makespacemadrid/Jarvis/Diseños3D/MakeSwitch/FreeCad/STL/DualColor/carcasa-mitades/bottom-a.obj

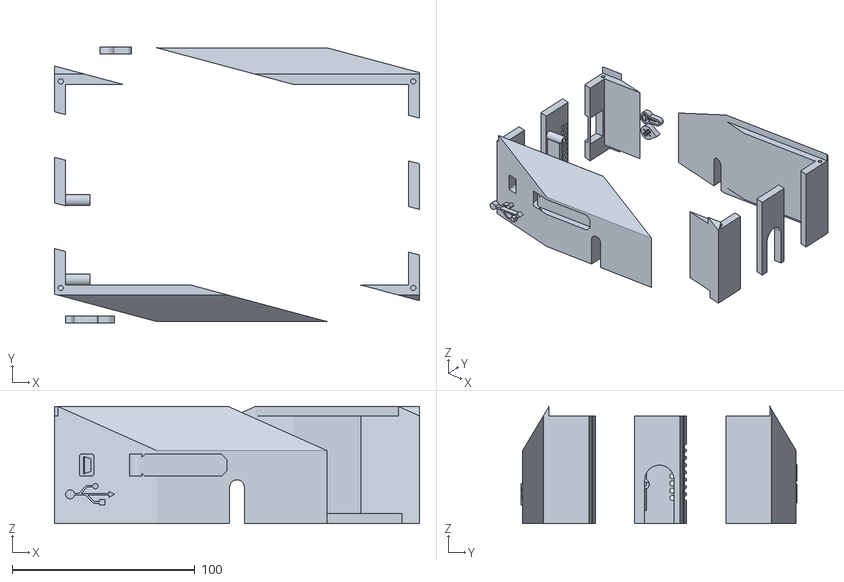
[picture p16: CAD file, 2015-12-14]
Diseños3D/MakeSwitch/FreeCad/STL/DualColor/carcasa-mitades/bottom-a.obj
200.0 x 151.3 x 64.2
