makespacemadrid/Jarvis/Diseños3D/MakeSwitch/FreeCad/STL/DualColor/carcasa_make-amarillo (repaired).stl

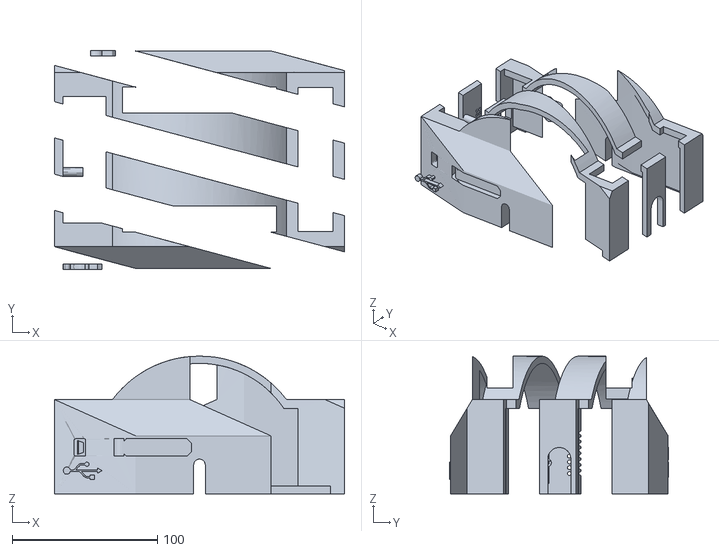
[picture p17: CAD file, 2015-11-29]
Diseños3D/MakeSwitch/FreeCad/STL/DualColor/carcasa_make-amarillo (repaired).stl
200.0 x 151.3 x 94.9
