makespacemadrid/Jarvis/Diseños3D/MakeSwitch/FreeCad/STL/palanca.obj

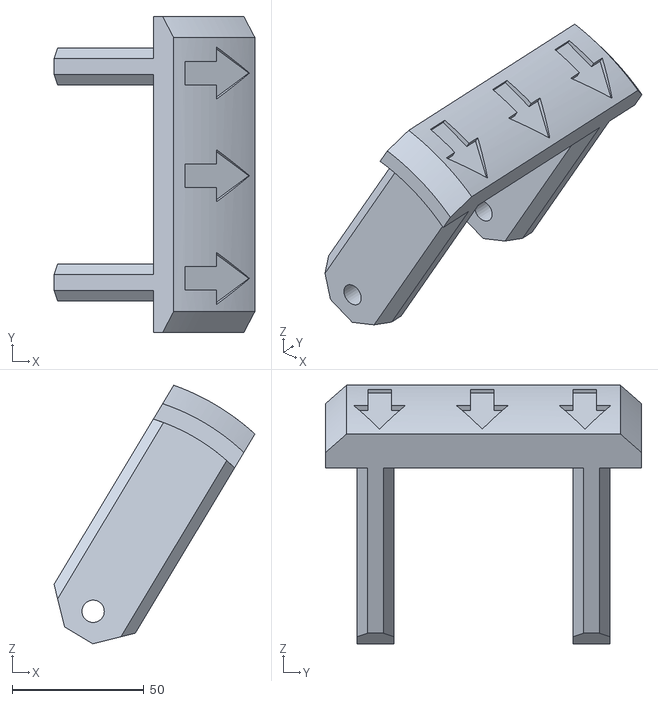
[picture p18: CAD file, 2015-11-29]
Diseños3D/MakeSwitch/FreeCad/STL/palanca.obj
76.3 x 120.0 x 98.2
