makespacemadrid/Jarvis/Diseños3D/MakeSwitch/FreeCad/STL/base.obj

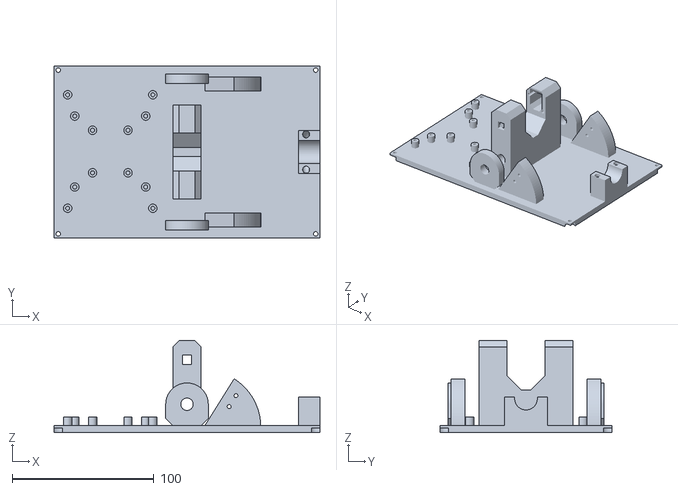
[picture p19: CAD file, 2015-11-29]
Diseños3D/MakeSwitch/FreeCad/STL/base.obj
187.5 x 121.5 x 65.0
