makespacemadrid/Jarvis/Diseños3D/MakeSwitch/FreeCad/STL/DualColor/carcasa-mitades/top.amf

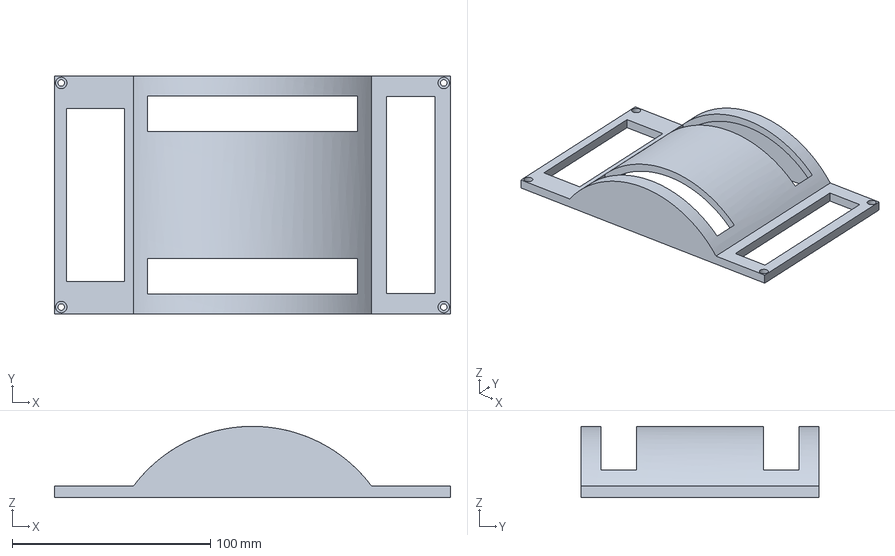
[picture p20: CAD file, 2015-12-14]
Diseños3D/MakeSwitch/FreeCad/STL/DualColor/carcasa-mitades/top.amf
200.0 x 120.0 x 36.0 mm
