makespacemadrid/Jarvis/Diseños3D/MakeSwitch/FreeCad/STL/DualColor/letras-transparente.obj

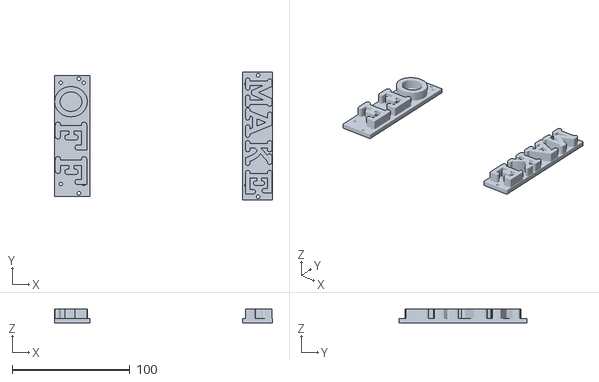
[picture p21: CAD file, 2015-11-29]
Diseños3D/MakeSwitch/FreeCad/STL/DualColor/letras-transparente.obj
185.4 x 108.9 x 12.0
