makespacemadrid/Jarvis/Diseños3D/MakeSwitch/FreeCad/STL/DualColor/carcasa-mitades/bottom-b (repaired).stl

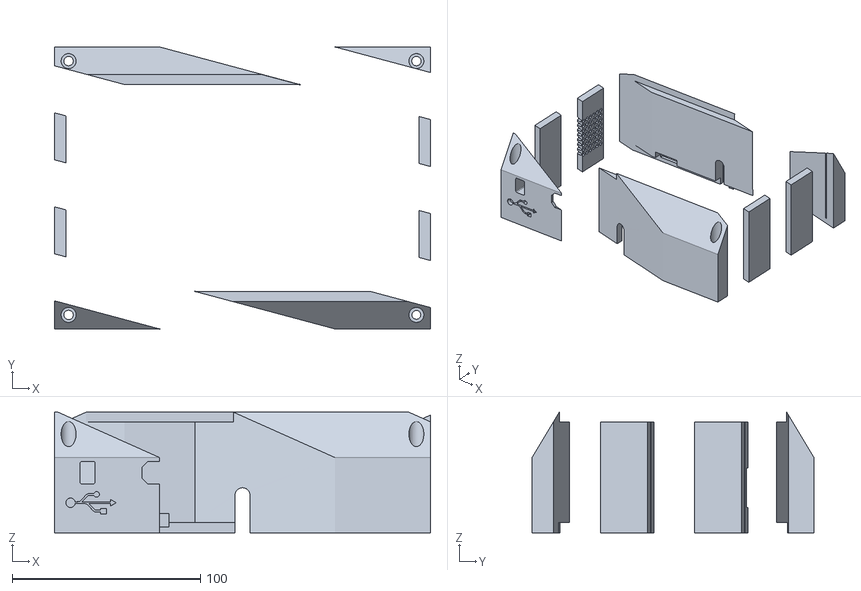
[picture p22: CAD file, 2015-12-14]
Diseños3D/MakeSwitch/FreeCad/STL/DualColor/carcasa-mitades/bottom-b (repaired).stl
200.0 x 150.0 x 64.2
