makespacemadrid/Jarvis/Diseños3D/MakeSwitch/FreeCad/STL/DualColor/palanca-flechas.obj

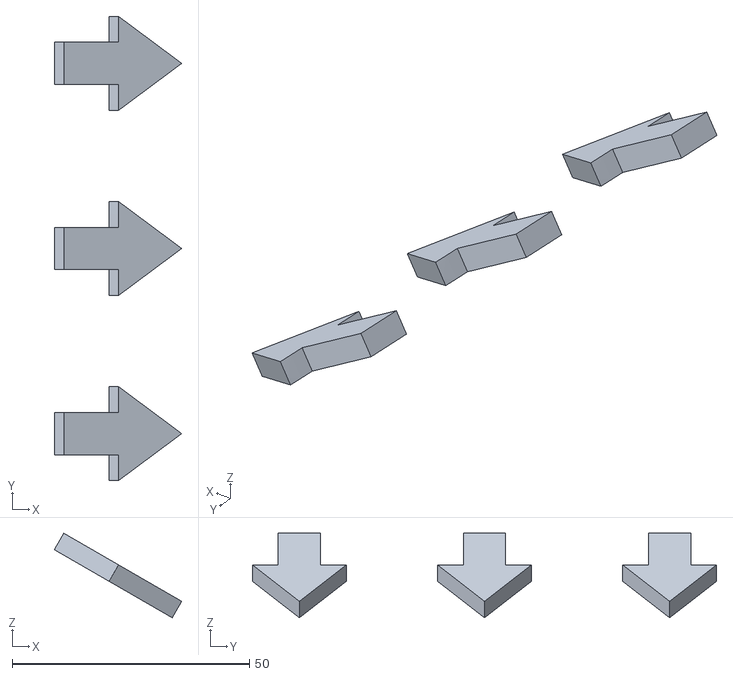
[picture p23: CAD file, 2015-11-29]
Diseños3D/MakeSwitch/FreeCad/STL/DualColor/palanca-flechas.obj
26.9 x 97.8 x 17.8
