makespacemadrid/Jarvis/Diseños3D/MakeSwitch/FreeCad/STL/reten.obj

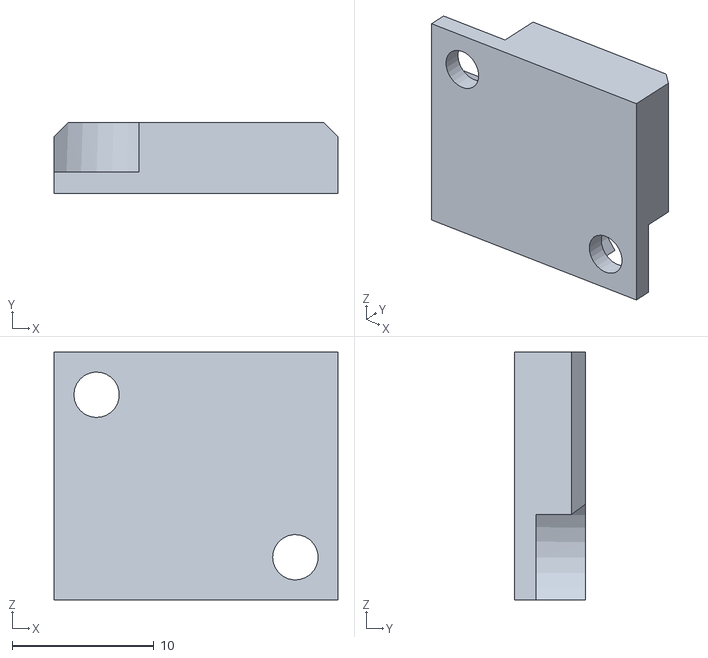
[picture p24: CAD file, 2015-11-29]
Diseños3D/MakeSwitch/FreeCad/STL/reten.obj
20.0 x 5.00 x 17.4
