makespacemadrid/Jarvis/Diseños3D/MakeSwitch/FreeCad/STL/empujador.obj

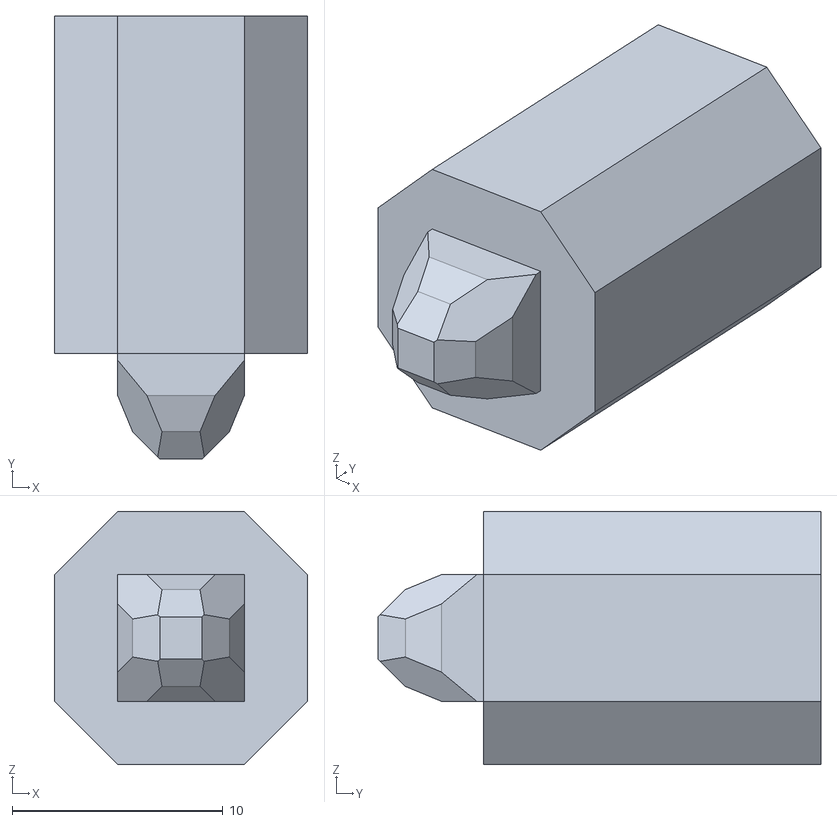
[picture p25: CAD file, 2015-11-29]
Diseños3D/MakeSwitch/FreeCad/STL/empujador.obj
12.0 x 21.0 x 12.0
