makespacemadrid/Jarvis/Diseños3D/MakeSwitch/FreeCad/STL/DualColor/carcasa-mitades/bottom-b.obj

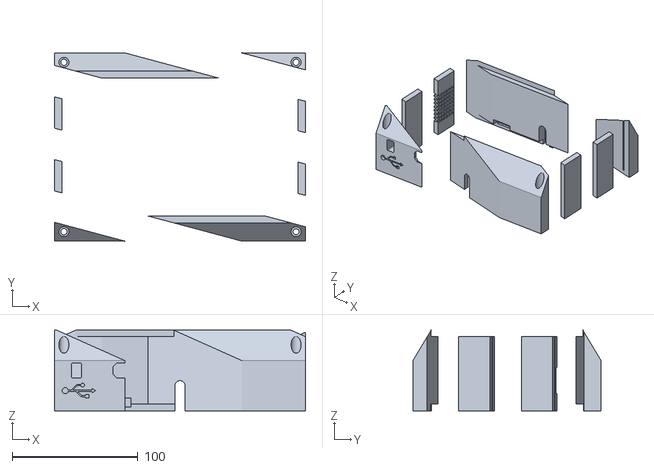
[picture p26: CAD file, 2015-12-14]
Diseños3D/MakeSwitch/FreeCad/STL/DualColor/carcasa-mitades/bottom-b.obj
200.0 x 150.0 x 64.2
