makespacemadrid/Jarvis/Diseños3D/MakeSwitch/FreeCad/STL/DualColor/letras-opaco.obj

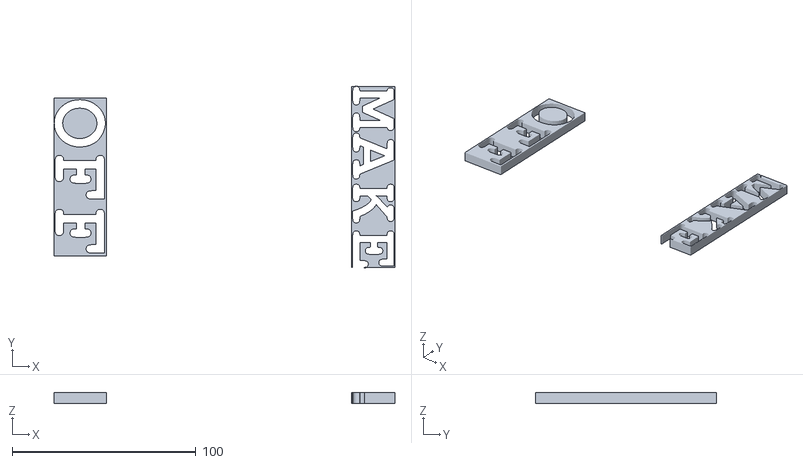
[picture p27: CAD file, 2015-11-29]
Diseños3D/MakeSwitch/FreeCad/STL/DualColor/letras-opaco.obj
185.4 x 98.6 x 6.00
