makespacemadrid/Jarvis/Software/JarvisFirmware/ws2812led.h

#ifndef LED
#define LED


#include <Adafruit_NeoPixel.h> //WTF hay que hacer el include en el ino!
#include <vector>
#include "nodeComponent.h"
//#include "ledMatrixIcons.h"

class ws2812Strip {
public:
    class led{ // clase led dentro de la clase Strip
    public:
      led(int r = 0, int g = 0, int b = 0, float bright = 1.0): m_r(r), m_g(r), m_b(b), m_bright(bright) {;}

      void setColor(uint8_t red =0,uint8_t green=0,uint8_t blue=0)
      {
          m_r = red;
          m_g = green;
          m_b = blue;
      }

      void dimm(int power)
      {
          float p = power /100;
          dimm(p);
      }

      void dimm(float factor = 0.75)
      {
          m_r *= factor;
          m_g *= factor;
          m_b *= factor;
      }

      void setBrightness(float b = 1.0)
      {
          m_bright = b;
      }

      void off()   {setColor(0,0,0);}
      void white() {setColor(200,200,200);}
      void red()   {setColor(230,0,0);}
      void green() {setColor(0,230,0);}
      void blue()  {setColor(0,0,230);}

      void setR(uint8_t val) {m_r = val;}
      void setG(uint8_t val) {m_g = val;}
      void setB(uint8_t val) {m_b = val;}

      int r()   {return m_r * m_bright;}
      int g()   {return m_g * m_bright;}
      int b()   {return m_b * m_bright;}

    private:
      uint8_t m_r;
      uint8_t m_g;
      uint8_t m_b;
      float   m_bright;
    };
  
  ws2812Strip(int pin = -1, int lednr = 25, float bright = 1.0) : m_pin(pin) , m_pixels(lednr, pin, NEO_GRB + NEO_KHZ800)
  {
    m_brightness = bright;
    if((isValid()))
    {
      for(int i = 0 ; i < lednr ; i++) m_leds.push_back(led());
    }
  }

  void setBrightness(int b)
  {
      m_brightness = b/100.0f;
      update();
  }

  void setBrightness(float b = 1.0)
  {
      m_brightness = b;
      update();
  }

  float brightness()
  {
      return m_brightness;
  }

  bool isValid() {return  (m_pin != -1);}

  std::vector<led> leds()&   {return m_leds;}

  led* getLed(int pos)
  {
    return &m_leds[pos];
  }

  void setup()
  {
    if(!isValid()) return;
    Serial.println("Setting up ws2812 strip....");
    m_pixels.begin();
    yield();
    test();
    off();
  }
  
  void update(){
    if(!isValid()) return;
    for(int i=0;i<m_leds.size();i++)
    {
        m_pixels.setPixelColor(i, (m_leds[i].r() * m_brightness) ,
                                  (m_leds[i].g() * m_brightness) ,
                                  (m_leds[i].b() * m_brightness) );
    }

    yield();
    m_pixels.show(); 
  }

  void off()
  {
    if(!isValid()) return;
    for( uint16_t i = 0 ; i < m_leds.size() ; i++)
    {
        m_leds[i].off();
    }
    update();
  }

  void setColor(uint8_t r,uint8_t g, uint8_t b){
    if(!isValid()) return;     
    for(int i=0;i<m_leds.size();i++)
    {
      m_leds[i].setColor(r,g,b);
    }
    update();
  }

  void test()
  {
    if(!isValid()) return;
    for( uint16_t i = 0 ; i < m_leds.size() ; i++)
    {
      m_leds[i].setColor(20,20,20);
      if(i%2 == 0)update();
    }
  }

private:
    std::vector<led>    m_leds;
    int                 m_pin;
    float               m_brightness;
    Adafruit_NeoPixel   m_pixels;
};


class ledGadget :  public nodeComponent
{
  public:
    enum animationType
    {
        animationNone,
        animationFade,
        animationGlow,
        animationBlink,
        animationCylon,
        animationChaoticLight,
        animationRainbow,
        animationScroll
    };

    ledGadget(ws2812Strip* m_parentStrip): m_strip(m_parentStrip) , m_bright(1.0)
    {
      m_capableEvents.push_back(E_ACTIVATED);
      m_capableEvents.push_back(E_DEACTIVATED);
      m_actions.push_back(A_ACTIVATE);
      m_actions.push_back(A_DEACTIVATE);
      m_actions.push_back(A_DIMM);
      m_actions.push_back(A_SET_COLOR);
      m_actions.push_back(A_SET_LEDS);
      m_actions.push_back(A_CYLON);
      m_actions.push_back(A_GLOW);
      m_actions.push_back(A_FADE);
    }
    
    void update()
    {
      if(!m_enabled) return;
      animate();
    }

    bool isValid() {return m_strip->isValid();}

    void deactivate()
    {
        fade();
    }

//gestion del array de leds

    void setLeds(std::vector<String>&  args)
    {
      if(!m_enabled) return;
      m_animationType = animationNone;
      for(int i = 0 ; i < args.size(); i+=3)
      {
          int n = i/3;
          if( n <= m_leds.size())
          {
            ws2812Strip::led* l = m_leds[n];
            l->setColor(args[i].toInt(),args[i+1].toInt(),args[i+2].toInt());
          }
      }
    }

    void setLeds(std::vector<uint8_t>  args)
    {
      if(!m_enabled) return;
      m_animationType = animationNone;
      for(int i = 0 ; i < args.size(); i+=3)
      {
          int n = i/3;
          if( n <= m_leds.size())
          {
            uint8_t r = args[i];
            uint8_t g = args[i+1];
            uint8_t b = args[i+2];
            ws2812Strip::led* l = m_leds[n];
            l->setColor(r,g,b);
          }
      }
    }

    void addLed(ws2812Strip::led* nLed)
    {
        m_leds.push_back(nLed);
    }

    void addLed(int start,int count,bool reverseOrder = false)
    {
        if(reverseOrder)
        {
            for(int i = start+count-1 ; i >= start ; i-- )
            {
                m_leds.push_back(m_strip->getLed(i));
            }
        }
        else
        {
            for(int i = start ; i < start+count ; i++ )
            {
                m_leds.push_back(m_strip->getLed(i));
            }
        }
    }

//efectos y animaciones

    virtual void off()
    {
        if(!m_enabled) return;
        resetAnimation();
        for(int i = 0 ; i < m_leds.size() ; i++)
            m_leds[i]->off();
        m_strip->update();
    }

    virtual void setColor(uint8_t r, uint8_t g, uint8_t b)
    {

        if(!m_enabled) return;
        resetAnimation();
        for(int i = 0 ; i < m_leds.size() ; i++)
        {
            m_leds[i]->setColor(r,g,b);
        }
        m_strip->update();
    }

    void dimm(uint8_t power)
    {
        if(power > 100) power = 100;
        setBrightness(power /100.0f);
    }

    void setBrightness(float b = 1.0)
    {
        m_bright = b;
        for(int i = 0 ; i < m_leds.size() ; i++)
        {
            m_leds[i]->setBrightness(b);
        }
        m_strip->update();
    }

    virtual void resetAnimation()
    {
        if(m_animationType == animationGlow)
        {
            setBrightness(1.0);
        }

        m_animationType = animationNone;
        m_counter1 = 0, m_counter2 = 0 ; m_counter3 = 0;
    }

    virtual void fade()
    {
        resetAnimation();
        m_animationType = animationFade;
    }

    virtual void glow()
    {
        resetAnimation();
        m_counter1 = 50, m_counter2 = 1 ; m_counter3 = 50;
        m_animationType = animationGlow;
    }

    virtual void blink()
    {
        resetAnimation();
        m_counter1 = 0, m_counter2 = 0 ; m_counter3 = 0;
        m_animationType = animationBlink;
    }

    virtual void cylon()
    {//animacion cylon
        resetAnimation();
        m_counter1 = 0, m_counter2 = 0 ; m_counter3 = 0;
        m_animationType = animationCylon;
    }

    virtual void chaoticLight()
    {
        resetAnimation();
        m_counter1 = 0, m_counter2 = 0 ; m_counter3 = 0;
        m_animationType = animationChaoticLight;
    }

    virtual void rainbow()
    {
        resetAnimation();
        m_counter1 = 0, m_counter2 = 0 ; m_counter3 = 0;
        m_animationType = animationRainbow;
    }

    virtual void scroll()
    {
        resetAnimation();
        m_counter1 = 0, m_counter2 = 0 ; m_counter3 = 0;
        m_animationType = animationScroll;
    }


    virtual void animate()
    {
        if(!m_enabled) return;
        if      (m_animationType == animationNone)
        {
            return;
        }else if(m_animationType == animationFade)
        {
            animateFade();
        }else if(m_animationType == animationGlow)
        {
            animateGlow();
        }else if(m_animationType == animationBlink)
        {
            animateBlink();
        }else if(m_animationType == animationCylon)
        {
            animateCylon();
        }else if(m_animationType == animationChaoticLight)
        {
            animateChaoticLigth();
        }else if(m_animationType == animationRainbow)
        {
            animateRainbow();
        }else if(m_animationType == animationScroll)
        {
            animateScroll();
        }

        m_strip->update();
    }


  protected:
    ws2812Strip*                    m_strip;
    std::vector<ws2812Strip::led*>  m_leds;
    animationType                   m_animationType = animationNone;
    float m_bright;

    uint8_t m_counter1;
    uint8_t m_counter2;
    uint8_t m_counter3;


    virtual void animateFade()
    {
        bool all_off = true;
        for(int i = 0 ; i < m_leds.size() ; i++)
        {
            if( (m_leds[i]->r() > 0) || (m_leds[i]->g() > 0) || (m_leds[i]->b() > 0) )
            {
                m_leds[i]->dimm();
                all_off=false;
            }
        }

        if(all_off)
        {
            m_events.push_back(E_DEACTIVATED);
            resetAnimation();
        }
    }

    virtual void animateGlow()
    {//contador 1 se usa contar la iteracion, y el 2 para la direccion(sumando/restando).
        if(m_counter2 == 0)
        {//sumando
            float bright = m_counter1/50.0;
            for(int i = 0 ; i < m_leds.size() ; i++)
            {
                m_leds[i]->setBrightness(bright);
            }

            if(m_counter1 == 50)
              m_counter2 = 1;
            else
              m_counter1++;
        }
        else
        {//restando
            float bright = m_counter1/50.0;
            for(int i = 0 ; i < m_leds.size() ; i++)
            {
                m_leds[i]->setBrightness(bright);
            }

            if(m_counter1 == 0)
                m_counter2 = 0;
            else
              m_counter1--;
        }
 //       Serial.print("C1: ");
 //       Serial.print(m_counter1);
 //       Serial.print(" :C2: ");
 //       Serial.print(m_counter2);
 //       Serial.print(" :C3: ");
 //       Serial.println(m_counter3);
 //       Serial.println("   ");
 //       Serial.println(m_leds[0]->b);
    }

    virtual void animateBlink()
    {

    }

    virtual void animateCylon()
    {//contador 1 para la iteracion, 2 para la direccion
        int min = 0;
        int max = m_leds.size();
        int count = max - min;

        if(m_counter2 == 0)//incrementando
        {
            int i = 0;
            for(int l = min ; l < max ; l++ )
            {
                ws2812Strip::led *led = m_leds[l];
                if(i == m_counter1)
                {
                   led->setColor(255,0,0);
                }
                else
                {
                    led->dimm();
                }

                if(m_counter1 >= max)
                {
                    m_counter1 = max;
                    m_counter2 = 1;
                    return;
                }
                else
                {
                    i++;
                }
            }
            m_counter1++;
        }else //decrementando
        {
            int i = count;
            for(int l = max-1 ; l >= min ; l-- )
            {
                ws2812Strip::led *led = m_leds[l];
                if(i == m_counter1)
                {
                   led->setColor(255,0,0);
                }
                else
                {
                    led->dimm();
                }

                if(m_counter1 <= min)
                {
                    m_counter1 = 0;
                    m_counter2 = 0;
                    return;
                }
                else
                {
                    i--;
                }
            }
            m_counter1--;
        }
    }
    virtual void animateChaoticLigth()
    {
        for(int i = 0 ; i < m_leds.size() ; i++)
        {
            int random = rand() % 3;
            if(random == 0)
                m_leds[i]->red();
            else if(random == 1)
                m_leds[i]->green();
            else if(random == 2)
                m_leds[i]->blue();
        }
    }


    virtual void animateRainbow()
    {
        if(m_counter1 > 256*5) m_counter1 = 0;

        for(uint16_t i = 0;  i < m_leds.size() ; i++)
        {
            uint16_t WheelPos = 255 - (((i * 256 / m_leds.size()) + m_counter1) & 255);
            if(WheelPos < 85)
            {
                m_leds[i]->setColor(255 - WheelPos * 3, 0, WheelPos * 3);
            }
            else if(WheelPos < 170)
            {
                WheelPos -= 85;
                m_leds[i]->setColor(0, WheelPos * 3, 255 - WheelPos * 3);
            }
            else
            {
                WheelPos -= 170;
                m_leds[i]->setColor(WheelPos * 3, 255 - WheelPos * 3, 0);
            }
            yield();
        }
        m_counter1 += 10;
    }

    virtual void animateScroll() {;}
};

class ledBar : public ledGadget
{
public:
    ledBar(ws2812Strip* parentStrip) : ledGadget(parentStrip), m_reversed(false) 
    {
      m_id = "ledBar";
    }
    void setReversed(bool reversed) {m_reversed = reversed;}

protected:
    bool m_reversed;

};


class ledStatusTrio : public ledBar
{
  public:
    ledStatusTrio(ws2812Strip* m_parentStrip, uint8_t mControllerLed, uint8_t wifiLed, uint8_t extraLed) :
       ledBar(m_parentStrip)
    {
        m_id = "ledStatusTrio";
        m_controllerLed = m_strip->getLed(mControllerLed);
        m_wifiLed       = m_strip->getLed(wifiLed);
        m_extraLed      = m_strip->getLed(extraLed);
        addLed(m_controllerLed);
        addLed(m_wifiLed);
        addLed(m_extraLed);
    }

    void animate()
    {
        if(!m_enabled) return;
        ledBar::animate();

        if(m_statusDecay)
            m_controllerLed->dimm();
        if(m_wifiStatusDecay)
            m_wifiLed->dimm();
        if(m_extraLedDecay)
            m_extraLed->dimm();
        m_strip->update();
    }

    void controllerInit()
    {
        if(!m_enabled)return;
        m_statusDecay = false;
        m_controllerLed->setColor(0,100,100);
    }

    void controllerOK()
    {
        if(!m_enabled)return;
        m_statusDecay = true;
        m_controllerLed->setColor(0,100,0);
    }

    void controllerError()
    {
        if(!m_enabled)return;
        m_statusDecay = false;
        m_controllerLed->setColor(100,0,0);
    }

    void wifiTX()
    {
        if(!m_enabled)return;
        m_wifiStatusDecay = true;
        m_wifiLed->setColor(0,100,0);
    }

    void wifiRX()
    {
        if(!m_enabled)return;
        m_wifiStatusDecay = true;
        m_wifiLed->setColor(100,0,0);
    }

    void wifiInit()
    {
        if(!m_enabled)return;
        m_wifiStatusDecay = false;
        m_wifiLed->setColor(100,100,0);
    }

    void wifiClient()
    {
        if(!m_enabled)return;
        m_wifiStatusDecay = false;
        m_wifiLed->setColor(0,100,100);
        m_wifiStatusColor = *m_wifiLed;
    }

    void wifiAutoConfig()
    {
        if(!m_enabled)return;
        m_wifiStatusDecay = false;
        m_wifiLed->setColor(100,0,100);
        m_wifiStatusColor = *m_wifiLed;
    }

    void wifiOK()
    {
        if(!m_enabled)return;
        *m_wifiLed = m_wifiStatusColor;
    }

    void wifiError()
    {
        if(!m_enabled)return;
        m_wifiStatusDecay = false;
        m_wifiLed->setColor(100,0,0);
    }

    void extraLedOK()
    {
        if(!m_enabled)return;
        m_extraLed->setColor(0,200,0);
    }

    void extraLedIdle()
    {
        if(!m_enabled)return;
        m_extraLed->setColor(0,0,200);
    }

    void extraLedError()
    {
        if(!m_enabled)return;
        m_extraLed->setColor(200,0,0);
    }

    void extraLedSetDecay(bool decay)
    {
        if(!m_enabled)return;
        m_extraLedDecay = decay;
    }

  private:
    ws2812Strip::led*   m_controllerLed;
    ws2812Strip::led*   m_wifiLed;
    ws2812Strip::led*   m_extraLed;
    ws2812Strip::led    m_wifiStatusColor;

    bool                m_statusDecay     = false;
    bool                m_wifiStatusDecay = false;
    bool                m_extraLedDecay   = false;
};


class ledMatrix : public ledBar
{
public:
    ledMatrix(uint8_t firstLednr, uint8_t cols, uint8_t rows, ws2812Strip* parentStrip,bool mirror = false, bool invertEachRow = false) : ledBar(parentStrip)
    {
        m_actions.push_back(A_DISPLAY);
        //Serial.println("Init matrix");
        for(int r = 0 ; r < rows ; r++)
        {
            //Serial.print("*row#");
            //Serial.println(r);

            m_matrix.push_back(std::vector<ws2812Strip::led*>());
            bool invertedRow = invertEachRow&&(r % 2 != 0);
            if(mirror) invertedRow = !invertedRow;

            int start = r*cols+firstLednr;
            int count = cols;

            if(invertedRow)
            {
                for(int i = start+count-1 ; i >= start ; i-- )
                {
                    //Serial.print(",");
                    //Serial.print(i);
                    ws2812Strip::led* l = m_strip->getLed(i);
                    //l->red();
                    //m_strip->update();
                    m_leds.push_back(l);
                    m_matrix[r].push_back(l);
                }
            }
            else
            {
                for(int i = start ; i < start+count ; i++ )
                {
                    //Serial.print(",");
                    //Serial.print(i);
                    ws2812Strip::led* l = m_strip->getLed(i);
                    //l->green();
                    //m_strip->update();
                    m_leds.push_back(l);
                    m_matrix[r].push_back(l);
                }
            }
            //Serial.println(".");
            yield();
        }

        m_id = "ws2812Matrix-";
        m_id +=cols;
        m_id +="x";
        m_id += rows;
        this->glow();
    }

    void deactivate()
    {   
        ledGadget::deactivate();
    }


    void display(std::vector<String>& args)
    {
        std::vector<uint8_t> argsInt;
        while(args.size())
        {
            argsInt.push_back(args[0].toInt());
            args.erase(args.begin());
        }
        yield();
        display(argsInt);
    }

    void display(std::vector<uint8_t>& args)
    {
         resetAnimation();

         if(args.size()%5 != 0) return; // los argumentos tienen que venir de 5 en 5. (x,y,r,g,b)
         File f = SPIFFS.open("displayBuffer", "w+");
         if (!f) {
             Serial.println("file open failed: displayBuffer");
             return;
         }
         uint8_t frows,fcols;

         if(f.size() > 2)
         {
             frows = f.read();
             fcols = f.read();
         }
         else
         {
             frows = 0;
             fcols = 0;
             f.write(0);
             f.write(0);
         }

         while (args.size())
         {
             int row = args[0];
             args.erase(args.begin());
             int col = args[0];
             args.erase(args.begin());
             uint8_t r = args[0];
             args.erase(args.begin());
             uint8_t g = args[0];
             args.erase(args.begin());
             uint8_t b = args[0];
             args.erase(args.begin());


             if(row < m_matrix.size() && col < m_matrix[row].size())
                 m_matrix[row][col]->setColor(r,g,b);
         }
        yield();
//        if(m_scrollImg[0].size() > m_matrix[0].size())
//             scroll();

         Serial.print("L-display done:, fm:");
         Serial.println(getFreeMem());
         m_strip->update();
    }

    void displayMatrix(std::vector<std::vector<ws2812Strip::led> > matrix)
    {
        if(matrix.size() == 0) return;

        resetAnimation();

        off();

        if( (matrix.size() > m_matrix.size()) || (matrix[0].size() > m_matrix[0].size()))
        {
            //m_scrollImg = matrix;
        }
        else
        {
            for(uint8_t row = 0 ; row < matrix.size() ; row++) //copia los valores que estan dentro del rango de la matriz
            {
                for(uint8_t col = 0 ; col < matrix[row].size() ; col++)
                {
                    if((row < m_matrix.size()) && (col < m_matrix[row].size()))
                    {
                        *m_matrix[row][col] = matrix[row][col];
                    }
                }
            }
        }
        update();
    }

    void writeMatrixToFile(String filename,const std::vector<std::vector<ws2812Strip::led> >& matrix)
    {
        if(!m_matrix.size() || !m_matrix[0].size())
        {
            Serial.println("Bad Matrix");
            return;
        }
        File f = SPIFFS.open(filename, "w");
        if (!f) {
            Serial.println("file open failed");
            return;
        }

//        f.close();//esto deberia de vaciar el fichero
//        f = SPIFFS.open(filename, "a");
        Serial.println("File Opened for write");

        uint8_t rows,cols;
        rows = matrix.size();
        cols = matrix[0].size();
        Serial.print("Saving matrix, ");
        Serial.print(rows);
        Serial.print("x");
        Serial.print(cols);
        Serial.print(".  ");
        Serial.print((m_matrix.size()*m_matrix[0].size()*3)+2);
        Serial.println("bytes");

        f.write(rows);
        f.write(cols);
        yield();

        for(int row = 0 ; row < rows ; row++)
        {
            for(int col = 0 ; col < cols ; col++)
            {
                uint8_t r = m_matrix[row][col]->r();
                uint8_t g = m_matrix[row][col]->g();
                uint8_t b = m_matrix[row][col]->b();
                f.write(r);
                f.write(g);
                f.write(b);
                yield();
            }
        }
        Serial.print("File Saved:");
        Serial.println(f.size());
        f.close();
        yield();
    }

    void displayFromFile(String filename)
    {
        off();

        File f = SPIFFS.open(filename, "r");
        if (!f) {
            Serial.println("file open failed");
            return;
        }
        uint16_t rows,cols;
        char a,b,c,d;
        a = f.read();
        b = f.read();
        c = f.read();
        d = f.read();
        rows = (a<< 8) | b;
        cols = (c<< 8) | d;
        uint8_t headerSize = sizeof(rows) + sizeof(cols);

        Serial.print("Loading Matrix, file:");
        Serial.print(filename);
        Serial.print(" rows:");
        Serial.print(rows);
        Serial.print(" cols:");
        Serial.println(cols);
        uint16_t expectedMatrixSize = (rows*cols*3)+headerSize;

        if(f.size() != expectedMatrixSize)
        {
            Serial.print("Wrong size:");
            Serial.print(f.size());
            Serial.print("/");
            Serial.println(expectedMatrixSize);
            return;
        }

        if( (rows >= m_matrix.size()) || (cols >= m_matrix.size()) )
        {
            m_file = filename;
            scroll();
        }

        for(int row = 0 ; row < m_matrix.size() ; row++)
        {
            for(int col = 0 ; col < m_matrix[row].size() ; col++)
            {
                if( (row < rows) && (col < cols) )
                {
                    uint16_t offset = (( (row*cols) + col) * 3) + headerSize;
                    f.seek(offset ,SeekSet);
                    uint8_t r = f.read();
                    uint8_t g = f.read();
                    uint8_t b = f.read();
                    m_matrix[row][col]->setColor(r,g,b);
                }
            }
        }
        m_strip->update();
        Serial.println("Done");
    }

protected:
    std::vector<std::vector<ws2812Strip::led*> >  m_matrix;
    String                                        m_file;

    void animateCylon()
    {
        //setLeds(ledMatrixIcons::cylonIcon16x16());
        //m_animationType = animationCylon;
        //contador 1 para la iteracion, 2 para la direccion
        int min = 0;
        int max = m_matrix[0].size();
        int count = max - min;
        //Serial.println(m_counter1);

        if(m_counter2 == 0)//incrementando
        {
            int i = 0;
            for(int l = min ; l < max ; l++ )
            {
                if(i == m_counter1)
                {
                    for(int c = 0 ; c < m_matrix.size() ; c++)
                    {
                        m_matrix[c][l]->setColor(255,0,0);
                    }
                }
                else
                {
                    for(int c = 0 ; c < m_matrix.size() ; c++)
                    {
                        m_matrix[c][l]->dimm();
                    }
                }

                if(m_counter1 >= count)
                {
                    m_counter1 = count;
                    m_counter2 = 1;
                    return;
                }
                else
                {
                    i++;
                }
            }
            m_counter1++;
        }else //decrementando
        {
            int i = count;
            for(int l = max-1 ; l >= min ; l-- )
            {
                if(i == m_counter1)
                {
                    for(int c = 0 ; c < m_matrix.size() ; c++)
                    {
                        m_matrix[c][l]->setColor(255,0,0);
                    }
                }
                else
                {
                    for(int c = 0 ; c < m_matrix.size() ; c++)
                    {
                        m_matrix[c][l]->dimm();
                    }
                }

                if(m_counter1 <= 0)
                {
                    m_counter1 = 0;
                    m_counter2 = 0;
                    return;
                }
                else
                {
                    i--;
                }
            }
            m_counter1--;
        }
    }

    void animateScroll()
    {
        File f = SPIFFS.open(m_file, "r");
        if (!f) {
            Serial.println("file open failed");
            return;
        }
        uint16_t rows,cols;
        char a,b,c,d;
        a = f.read();
        b = f.read();
        c = f.read();
        d = f.read();
        rows = (a<< 8) | b;
        cols = (c<< 8) | d;
        uint8_t headerSize = sizeof(rows) + sizeof(cols);


        for(int row = 0 ; row < m_matrix.size() ; row++)
        {
            for(int col = 0 ; col < m_matrix[row].size() ; col++)
            {
                if( (row < rows) && (col+m_counter1 < cols) )
                {
                    uint16_t offset = (( (row*cols) + col+m_counter1) * 3) + headerSize;
                    f.seek(offset ,SeekSet);
                    uint8_t r = f.read();
                    uint8_t g = f.read();
                    uint8_t b = f.read();
                    m_matrix[row][col]->setColor(r,g,b);
                }
            }
        }


        if      (m_counter1 == cols-m_matrix[0].size())
            m_counter2 = 1;//contador 2 para controlar la direccion
        else if (m_counter1 == 0)
            m_counter2 = 0;

        if(m_counter3 > 3)//contador 3 para hacer un divisor y que el efecto sea mas lento
        {
            m_counter3 = 0;
            if(m_counter2 == 0)
                m_counter1++;//contador 1 para el offset de la imagen.
            else
                m_counter1--;
        }

        m_counter3++;

    }
};

#endif
