makespacemadrid/Jarvis/Software/JarvisFirmware/ledMatrixIcons.h

#ifndef LEDMATRIXICONS_H
#define LEDMATRIXICONS_H

#include <vector>
#include "ws2812led.h"

#define BIG_FLASH
#ifdef BIG_FLASH


class ledMatrixIcons
{
public:

    static std::vector<uint8_t> wifiGreenIcon16x16()
    {
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
        return convertArrayToLedMatrix(makespaceBigicon,10,72);
    }

    static std::vector<std::vector<ws2812Strip::led> > convertArrayToLedMatrix(const uint8_t* input,uint16_t rows, uint16_t cols)
    {
        //uint16_t arraySize = sizeof(input) / sizeof(uint16_t);
        uint16_t arraySize = cols*rows*3;
        //Serial.print("Array has:");
        //Serial.print(cols);
        //Serial.print("x");
        //Serial.println(rows);

        std::vector<std::vector<ws2812Strip::led> > result;
        uint16_t pos = 0;
        for(int y = 0 ; (y < rows) && (pos < arraySize) ; y++)
        {
            result.push_back(std::vector<ws2812Strip::led>());
            for(int x = 0 ; (x < cols) && (pos < arraySize) ; x++)
            {
                if(arraySize >= pos+3)
                {
                    ws2812Strip::led l;
                    l.setR(input[pos++]);
                    l.setG(input[pos++]);
                    l.setB(input[pos++]);
                    result[y].push_back(l);
                }
            }
        }
        return result;
    }

};


#endif
#endif // LEDMATRIXICONS_H
