makespacemadrid/Jarvis/Software/JarvisServer/jarvisServer/sjarvisnodeserver.h

#ifndef SJARVISNODESERVER_H
#define SJARVISNODESERVER_H

#include "sjarvisnode.h"
#include <QTcpServer>

class sJarvisNodeServer : public QTcpServer
{
    Q_OBJECT
public:
    explicit sJarvisNodeServer(QObject *parent = 0);
    QList<sJarvisNode*>& nodes() {return m_nodes;}

protected:
    QList<sJarvisNode*> m_nodes;

    void addNode(sJarvisNode* nNode);

signals:
    void new_node(sJarvisNode* nNode);
protected slots:
    void handleNewConn();
public slots:
    void connectNode(QString host, qint16 port);
    void validateClient(QTcpSocket *client);
    void nodeReady();
    void removeNode(QObject *obj);


};

#endif // SJARVISNODESERVER_H
