makespacemadrid/Jarvis/Software/JarvisServer/common/gnodecomponentwidget.h

#ifndef GNODECOMPONENTWIDGET_H
#define GNODECOMPONENTWIDGET_H

#include <QGroupBox>
#include "sjarvisnodecomponent.h"
#include "gblinkwidget.h"

namespace Ui {
class gNodeComponentWidget;
}

class gNodeComponentWidget : public QGroupBox
{
    Q_OBJECT

public:
    explicit gNodeComponentWidget(sJarvisNodeComponent* comp, QWidget *parent = 0);
    ~gNodeComponentWidget();

private:
    sJarvisNodeComponent*     m_component;
    Ui::gNodeComponentWidget *ui;

private slots:
    void sendImage();
    void selectComponentColor();
    void openRtttlPlayer();
};

#endif // GNODECOMPONENTWIDGET_H
